monofuel/Prusa3/src/y-idler.scad

// PRUSA iteration3
// Y idler
// GNU GPL v3
// Josef Průša <iam@josefprusa.cz> and contributors
// http://www.reprap.org/wiki/Prusa_Mendel
// http://prusamendel.org


module y_idler_base(){
 translate(v = [0,0,0]) cylinder(h = 19, r=8);	
 translate(v = [0,20,0]) cylinder(h = 19, r=8);
 translate(v = [0,10,9.5]) cube(size = [16,20,19], center=true);
 translate(v = [-4,10,9.5]) cube(size = [8,16+20,19], center=true);
}

module y_idler_holes(){
 translate(v = [0,0,-1]) cylinder(h = 120, r=2.5);	
translate([0,20,20]) rotate([0,90,0]) teardrop(r=4.4,h=21,$fn=30);
 translate(v = [0,0,4]) cylinder(h = 11, r=12);
}

module teardrop (r=8,h=20)
{
rotate([-270,0,90])
linear_extrude(height=h)
{
circle(r=r);
polygon(points=[[0,0],[r*cos(30),r*sin(30)],[0.5*r,r],[-0.5*r,r],[-r*cos(30),r*sin(30)]],
paths=[[0,1,2,3,4]]);
}
}


// Final part
module y_idler(){
 translate(v = [0,0,8])rotate([0,-90,0]) difference(){
  y_idler_base();
  y_idler_holes();
 }
}

y_idler();
